schuetzenring-AEH/Vogelstimmen/hardware/V3.0/docs/zaehler_lieferanten_links.md

# Lieferanten — PCB-Mini 12 V Impulszähler (V3.0)

Zielteil: **~30×42 mm**, **12 V DC**, Litzen oder PCB-Pins → J5 (One-Shot).  
**Nicht** Panel-CSK/875.

## Sofort bestellbar (kleine Stückzahl)

### 1) Trumeter E660 / E760 — 12 V (empfohlen für 6–10 Stk.)

| | |
|--|--|
| **Was** | Kompakter Non-Reset Totalizer, ~28 g, Continuous ON ok, One-Shot ok |
| **Bestellform** | z. B. **E660** + Mounting **RT** (Rear + Terminal Pins) oder Litzen-Variante + **DC12** |
| **Shop / Quote** | [Trumeter E660/E760](https://www.trumeter.com/product/e660-e760/) → „Get a Quote“ (Europe) |
| **Alt. US-Shop** | [ITM / GlobalTestSupply E760 12 V](https://www.globaltestsupply.com/product/trumeter-e760-series-non-reset-totalizing-counter-e760mrt20dc12) |
| **Datenblatt-Logik** | `E660` = 6 Stellen, `E760` = 7 Stellen; `RT` = PCB-Pins; `DC12` |

Litzen-Variante an J5 anlöten; Pin-Variante mit kurzen Drähten auf J5.

### 2) Ningbo Yaoye — Alibaba (günstig, China)

| | |
|--|--|
| **Shop** | [yaoye.en.alibaba.com](https://yaoye.en.alibaba.com/) |
| **Web** | [yaooye.com](http://www.yaooye.com/) |
| **Anfrage** | „6/7 digit electromagnetic counter **DC12V**, **PCB pin or flying lead**, size ~30×40 mm, **MOQ ≤20**“ |
| **Modelle** | Yaoye-5 / 5B / ähnlich (Spannung **12 V** fest bestellen) |

Vor Kauf: Foto + Maßskizze Pins/Litzen verlangen.

### 3) KEP / Precision Sales — EP770 MRT 12 V

| | |
|--|--|
| **Was** | 7-digit, PCB-Pins, Continuous ON, ~16 g |
| **Code** | `EP770 MRT 12VDC 25CPS` |
| **Kontakt** | [Precision Sales – Vending/Gaming Meters](https://www.precisionsales.com/counter-timer-ratemeter/panel-meter/vending_gaming.htm) |
| **PDF** | [EP770 Datasheet](https://www.precisionsales.com/counter-timer-ratemeter/keppdf/EP770_DS.pdf) |

## Original Line Seiki MZ (nur bei größerer Menge)

| | |
|--|--|
| **Teil** | **MZ-600 DC12V** (Litzen) oder **MZ-602 DC12V** (Pins 12,7 mm) |
| **Hersteller** | [lineseiki.com – MZ Series](https://www.lineseiki.com/product/2104/) |
| **Bestellung** | [Kontaktformular](https://www.lineseiki.com/contact-inquiry/) oder **webtrade@line.co.jp** |
| **Händler JP** | [Kouei Trading – MZ Quote](https://koueitrading.com/global/product/line-seiki-mz-series-electromagnetic-counters/) |
| **Haken** | Hersteller nennt oft **MOQ ~100** — für 6–10 Stk. unpraktisch |

## Praktische Empfehlung für Vogelstimmen

1. **Jetzt:** Trumeter **E660 … DC12** (Quote Europe) **oder** Yaoye 12 V Litzen (Alibaba, 10 Stk.).  
2. **Wenn Serie ≥100:** Line Seiki **MZ-602 DC12V**.  
3. Anschluss immer an **J5** (+/`12V_SW`, −/`CNT_LO`).

## Was nicht suchen

- DigiKey/Mouser/RS: MZ-602 praktisch **nicht** lagernd  
- CSK6/875 Panel: zu groß für euer Gehäuse
