schuetzenring-AEH/Vogelstimmen/docs/mbse_sysml.md

# MBSE / SysML-Sicht (Mermaid) — Rev 2.5

**Werkzeug:** Kein Cameo/Capella — SysML-Semantik als Markdown/Mermaid (Digital Thread light).

---

## 1. Requirement Diagram (Konzept)

```
F02 Taster→Stimme ──satisfy──> SF-04 Abspielen
E02 Idle <100µA ──satisfy──> SF-11 Ruhestrom
E02 ──derive──> E-LATCH-01
F-01 Review ──refine──> SYS-05 Domain-Trennung
```

Vollständige Tabellen: `traceability.md`, `anforderungen.md`.

---

## 2. BDD — Blöcke

Siehe `systemarchitektur.md` §2 (B1–B8).

```mermaid
graph TB
  SYS[Vogelstimmen Elektronik]
  SYS --> B1[B1 Eingangsschutz]
  SYS --> B2[B2 Latch]
  SYS --> B3[B3 Buck]
  SYS --> B4[B4 Audio]
  SYS --> B5[B5 Zähler]
  SYS --> B6[B6 Taster]
  SYS --> B7[B7 SPK]
  SYS --> B8[B8 LED]
```

---

## 3. IBD — Hauptflüsse

```
BAT → B1 → 12V_PROT → B2 → 12V_SW → B3 → 5V → B4,B5
Taster → B6 → IOx / BTN_OR → B2,B4
B4 BUSY → B2 Release
B4 → B7 SPK
12V_SW → B8 → LEDs
```

---

## 4. Use Case Diagram

Akteure & UC: `use_cases.md`.

---

## 5. State Machine (Versorgung)

```
Idle (Latch aus, ~12µA)
  --Taste--> SetPulse
  -- > PowerUp/Boot
  --Flanke--> Playing
  --BUSY+RC--> Release
  --> Idle
```

Simuliert in `simulation/`.

---

## 6. Sequence / Activity

`use_cases.md` §5–6.

---

## 7. Parametric (Energie — Analyse)

| Parameter | Wert | Quelle |
|---|---|---|
| Idle | ≈12 µA | E-RPP-01 / Sim |
| Ziel E02 | <100 µA | Lastenheft |
| Batterie | ~30 Ah (Annahme) | E03 Analyse in traceability |
| Play-Strom | Modul ≤60 mA + SPK + LED | parts.js / Spec |

Kein vollständiges Parametric Diagram Tool — Rechnung dokumentiert.

---

## 8. Digital Twin

Dokumentebene: `digitaler_zwilling.md`  
Verhaltens-Twin: `simulation/` (DC-Arbeitspunkte + Phasen, kein SPICE).
