schuetzenring-AEH/Vogelstimmen/hardware/V2.5-final/simulation/index.html

# Vogelstimmenkasten

Platinen-Simulation Rev 2.5 — Ohm/FET/Zener real, Buck · DY-SV17F (Idle 14 mA / Betrieb ≤60 mA) · Kübler. Respin: D15–D22, R5=0 Ω, R12/R13/C4. Werte in js/parts.js.

Reset Pause Kurzdruck-Miss Hold 400 ms Tempo 4.0×

Phase—

IBAT—

Track—

Zähler0

blau = Passiv / Stiftleiste Bahn grau ≈0 grün <1 mA gelb <50 mA rot ≥50 mA ⊙ Via (Durchkontaktierung)

Leiterbahnen aus KiCad v2.5 (pcb_tracks.json, 32 Vias). Farbe = Strom im Netz. Klick auf Bauteil → Detail.

## Netze

## Bauteile U / I / P

Ref | BG | Wert | Zustand | U | I | Spec

Schließen

### Erklärung

#### System — Hauptbaugruppen

#### Baugruppe — Funktion & Schnittstellen

#### Was die Baugruppe tut

#### Was dieses Bauteil tut
