schuetzenring-AEH/Vogelstimmen/rev1_archiv/hardware/report.txt

Aktualisiere Symbol C2 von "vogelstimmen:C" nach "vogelstimmen:C": OK
Aktualisiere Symbol C4 von "vogelstimmen:C" nach "vogelstimmen:C": OK
Aktualisiere Symbol J1 von "vogelstimmen:Conn_01x02" nach "vogelstimmen:Conn_01x02": OK
Aktualisiere Symbol Q1 von "vogelstimmen:Q_PMOS" nach "vogelstimmen:Q_PMOS": OK
Aktualisiere Symbol F1 von "vogelstimmen:Fuse" nach "vogelstimmen:Fuse": OK
Aktualisiere Symbol D1 von "vogelstimmen:D" nach "vogelstimmen:D": OK
Aktualisiere Symbol C1 von "vogelstimmen:C" nach "vogelstimmen:C": OK
Aktualisiere Symbol U4 von "vogelstimmen:TPS62203" nach "vogelstimmen:TPS62203": OK
Aktualisiere Symbol U5 von "vogelstimmen:SGM809" nach "vogelstimmen:SGM809": OK
Aktualisiere Symbol L1 von "vogelstimmen:L" nach "vogelstimmen:L": OK
Aktualisiere Symbol R11 von "vogelstimmen:R" nach "vogelstimmen:R": OK
Aktualisiere Symbol C3 von "vogelstimmen:C" nach "vogelstimmen:C": OK
Aktualisiere Symbol U1 von "vogelstimmen:WT588D-16P" nach "vogelstimmen:WT588D-16P": OK
Aktualisiere Symbol R9 von "vogelstimmen:R" nach "vogelstimmen:R": OK
Aktualisiere Symbol C6 von "vogelstimmen:C" nach "vogelstimmen:C": OK
Aktualisiere Symbol C8 von "vogelstimmen:C" nach "vogelstimmen:C": OK
Aktualisiere Symbol C9 von "vogelstimmen:C" nach "vogelstimmen:C": OK
Aktualisiere Symbol C18 von "vogelstimmen:C" nach "vogelstimmen:C": OK
Aktualisiere Symbol C7 von "vogelstimmen:C" nach "vogelstimmen:C": OK
Aktualisiere Symbol R2 von "vogelstimmen:R" nach "vogelstimmen:R": OK
Aktualisiere Symbol R4 von "vogelstimmen:R" nach "vogelstimmen:R": OK
Aktualisiere Symbol R12 von "vogelstimmen:R" nach "vogelstimmen:R": OK
Aktualisiere Symbol R5 von "vogelstimmen:R" nach "vogelstimmen:R": OK
Aktualisiere Symbol R6 von "vogelstimmen:R" nach "vogelstimmen:R": OK
Aktualisiere Symbol J2 von "vogelstimmen:Conn_01x02" nach "vogelstimmen:Conn_01x02": OK
Aktualisiere Symbol R7 von "vogelstimmen:R" nach "vogelstimmen:R": OK
Aktualisiere Symbol U3 von "vogelstimmen:PAM8403" nach "vogelstimmen:PAM8403": OK
Aktualisiere Symbol R1 von "vogelstimmen:R" nach "vogelstimmen:R": OK
Aktualisiere Symbol R8 von "vogelstimmen:R" nach "vogelstimmen:R": OK
Aktualisiere Symbol U2 von "vogelstimmen:W25Q128" nach "vogelstimmen:W25Q128": OK
Aktualisiere Symbol C10 von "vogelstimmen:C" nach "vogelstimmen:C": OK
Aktualisiere Symbol C5 von "vogelstimmen:C" nach "vogelstimmen:C": OK
Aktualisiere Symbol J3 von "vogelstimmen:Conn_01x10" nach "vogelstimmen:Conn_01x10": OK
Aktualisiere Symbol R3 von "vogelstimmen:R" nach "vogelstimmen:R": OK
Aktualisiere Symbol R13 von "vogelstimmen:R" nach "vogelstimmen:R": OK
Aktualisiere Symbol J5 von "vogelstimmen:Conn_01x02" nach "vogelstimmen:Conn_01x02": OK
Aktualisiere Symbol C11 von "vogelstimmen:C" nach "vogelstimmen:C": OK
Aktualisiere Symbol C12 von "vogelstimmen:C" nach "vogelstimmen:C": OK
Aktualisiere Symbol C14 von "vogelstimmen:C" nach "vogelstimmen:C": OK
Aktualisiere Symbol C17 von "vogelstimmen:C" nach "vogelstimmen:C": OK
Aktualisiere Symbol C13 von "vogelstimmen:C" nach "vogelstimmen:C": OK
Aktualisiere Symbol #FLG01 von "power:PWR_FLAG" nach "power:PWR_FLAG": OK
Aktualisiere Symbol C15 von "vogelstimmen:C" nach "vogelstimmen:C": OK
Aktualisiere Symbol C16 von "vogelstimmen:C" nach "vogelstimmen:C": OK
Aktualisiere Symbol R10 von "vogelstimmen:R" nach "vogelstimmen:R": OK
Aktualisiere Symbol Q2 von "vogelstimmen:Q_NMOS" nach "vogelstimmen:Q_NMOS": OK
Aktualisiere Symbol #FLG02 von "power:PWR_FLAG" nach "power:PWR_FLAG": OK
Aktualisiere Symbol #FLG03 von "power:PWR_FLAG" nach "power:PWR_FLAG": OK
Aktualisiere Symbol J4 von "vogelstimmen:Conn_01x04" nach "vogelstimmen:Conn_01x04": OK
