schuetzenring-AEH/Vogelstimmen/docs/pcb-platzierungsplan-optimiert.png

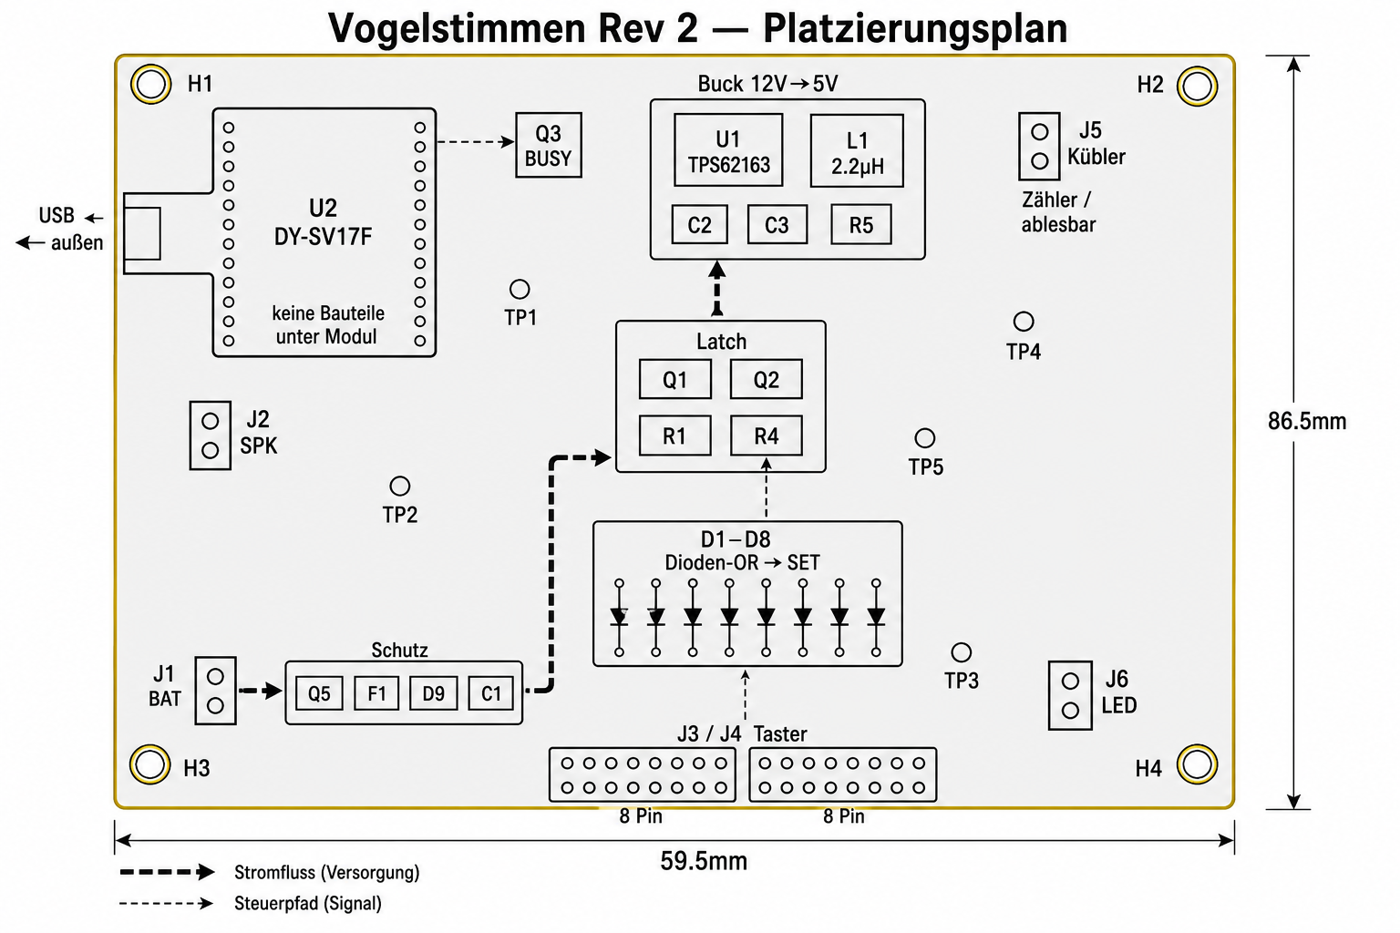
docs/pcb-platzierungsplan-optimiert.png
