schuetzenring-AEH/Vogelstimmen/hardware/V2.5-final/jlcpcb_production_review/13016843a_y4/yg/GBR_12090842_1_snapshot.png

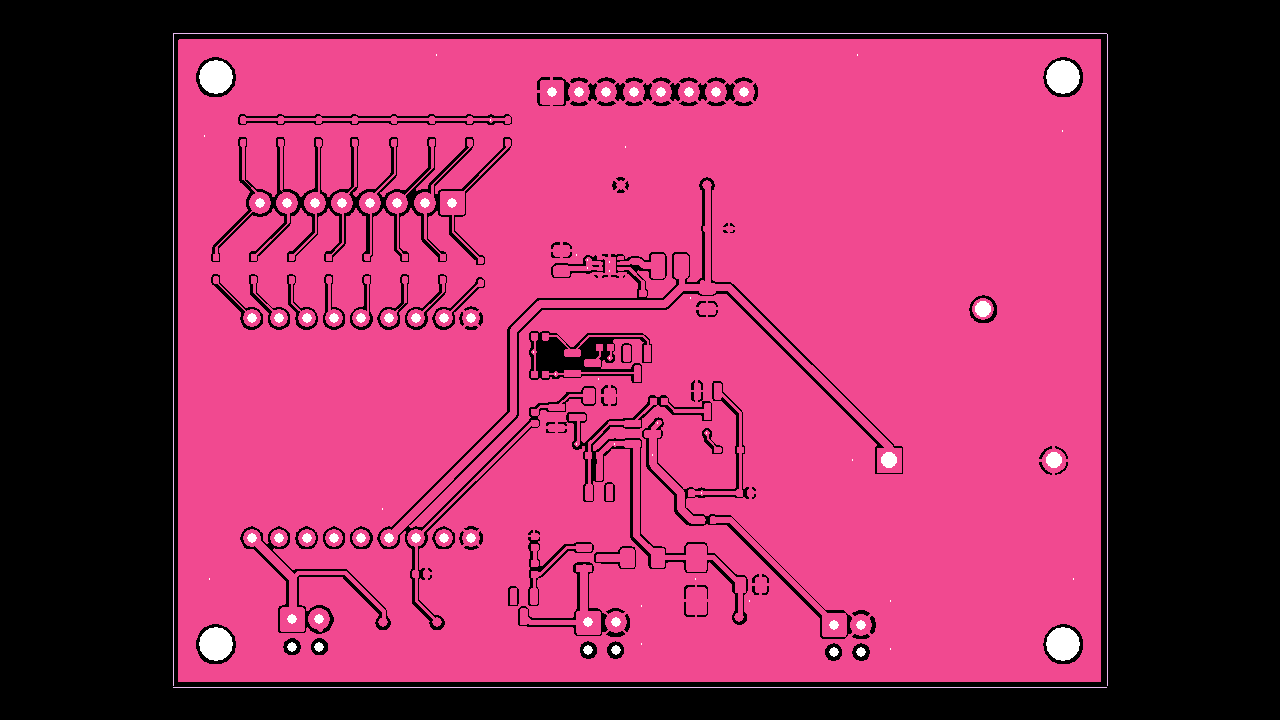
hardware/V2.5-final/jlcpcb_production_review/13016843a_y4/yg/GBR_12090842_1_snapshot.png
