schuetzenring-AEH/Vogelstimmen/hardware/V3.0/docs/h635_crop_bot_right.png

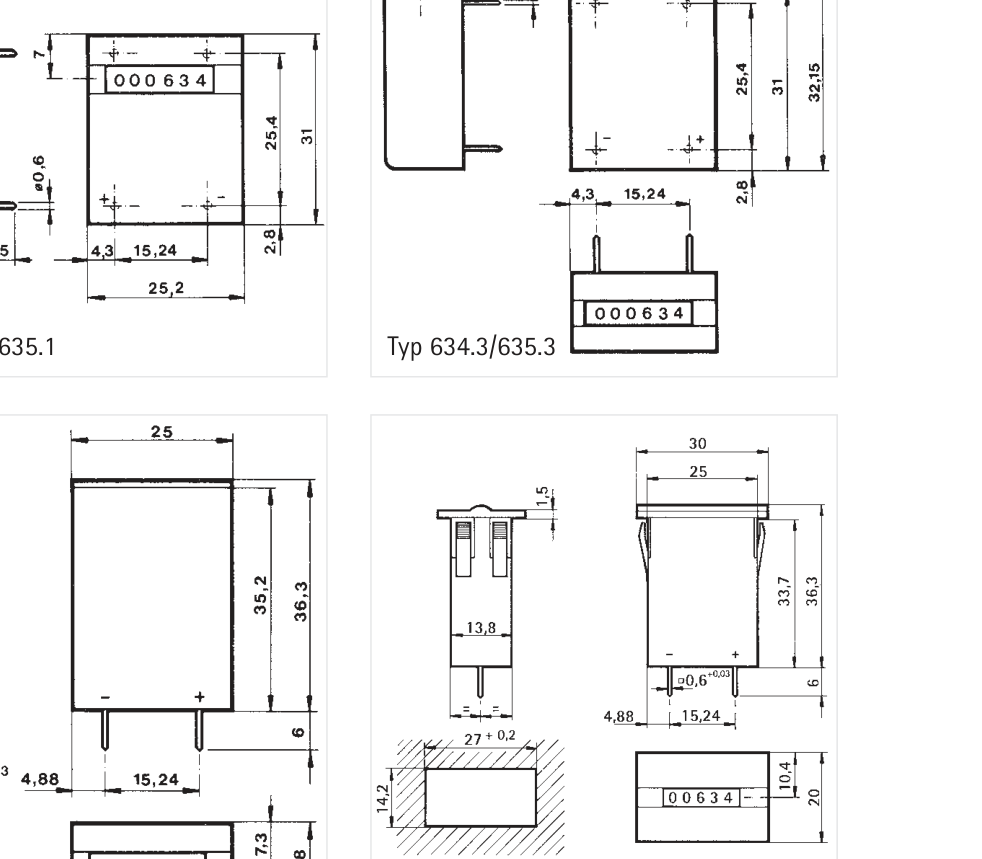
hardware/V3.0/docs/h635_crop_bot_right.png
