schuetzenring-AEH/Vogelstimmen/hardware/V3.0/docs/h635_crop_top_right.png

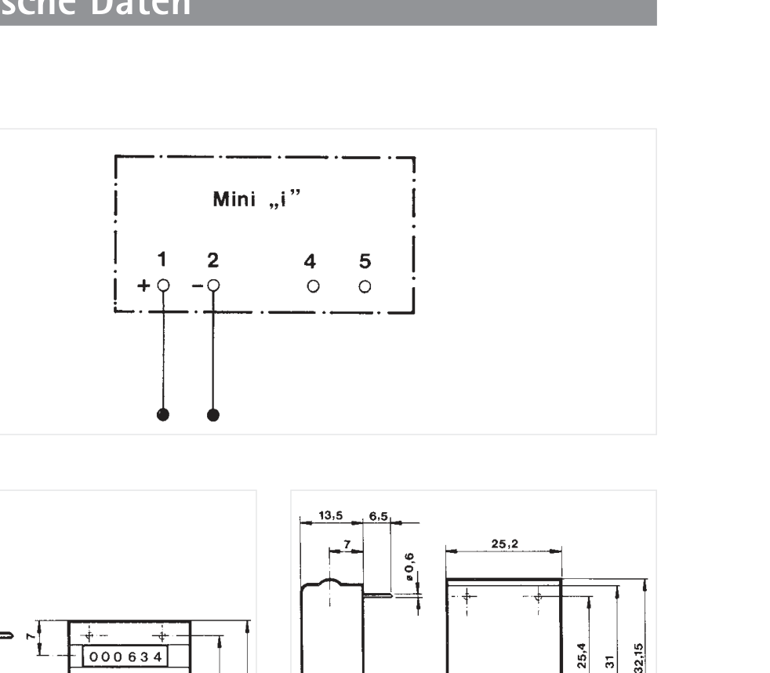
hardware/V3.0/docs/h635_crop_top_right.png
