schuetzenring-AEH/Vogelstimmen/hardware/V3.0/docs/h635_other_tight.png

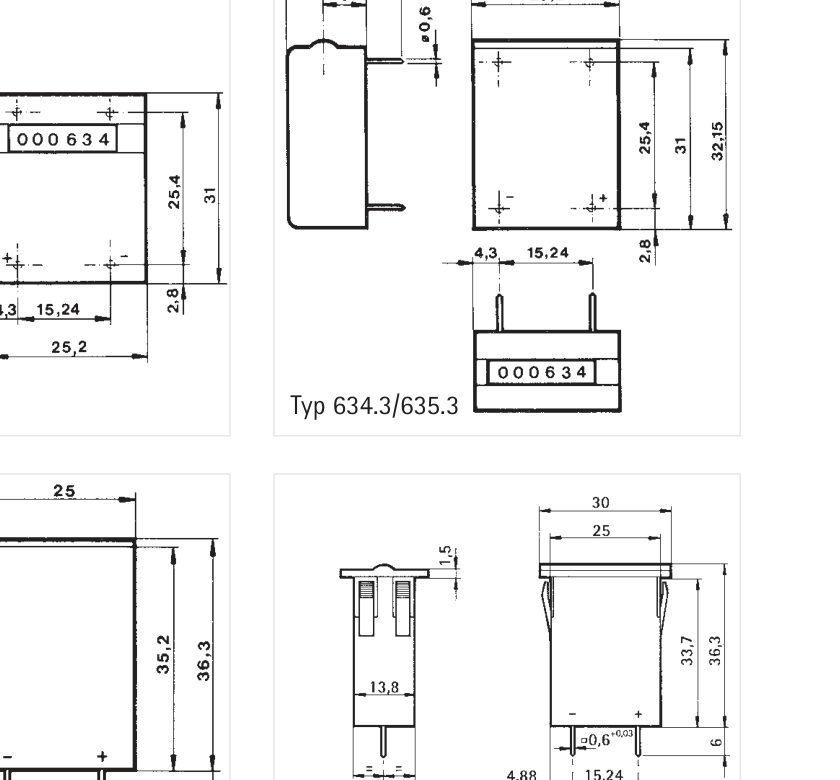
hardware/V3.0/docs/h635_other_tight.png
