schuetzenring-AEH/Vogelstimmen/hardware/V3.0/docs/Hengstler_634_635_de.pdf_1.png

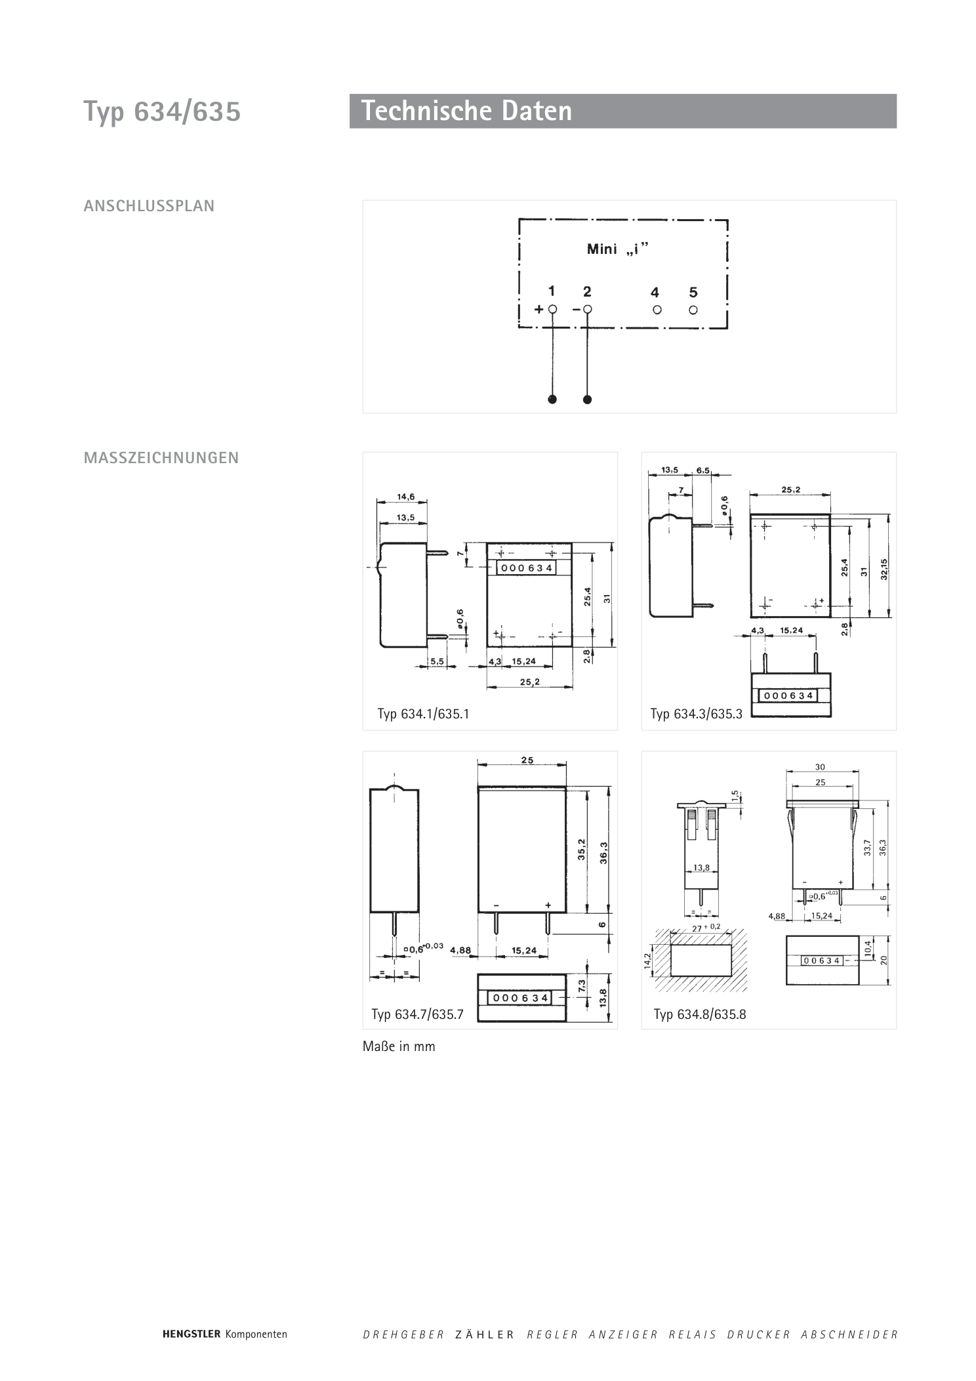
hardware/V3.0/docs/Hengstler_634_635_de.pdf_1.png
